koenver/ADE9000-ESP-32-energy-monitor-phasor-measurement-unit-modulair/hardware/pictures/IMG_0277.jpg

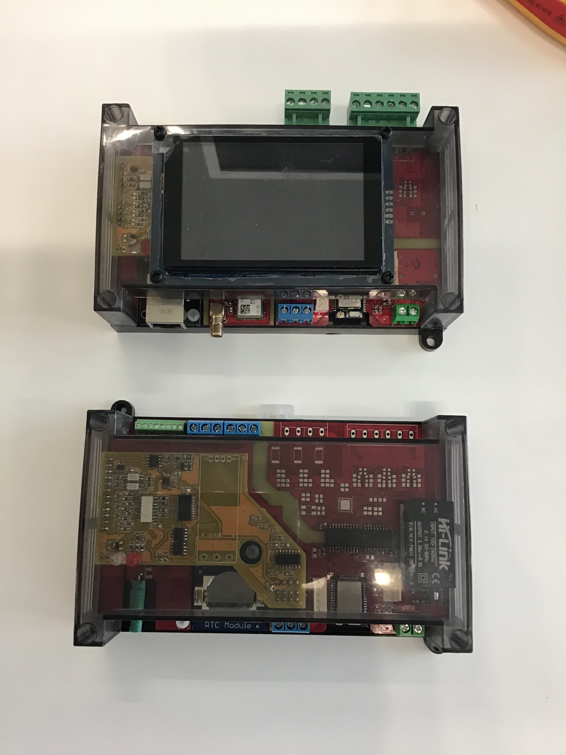
hardware/pictures/IMG_0277.jpg
