koenver/ADE9000-ESP-32-energy-monitor-phasor-measurement-unit-modulair/hardware/pictures/IMG_1338.JPG

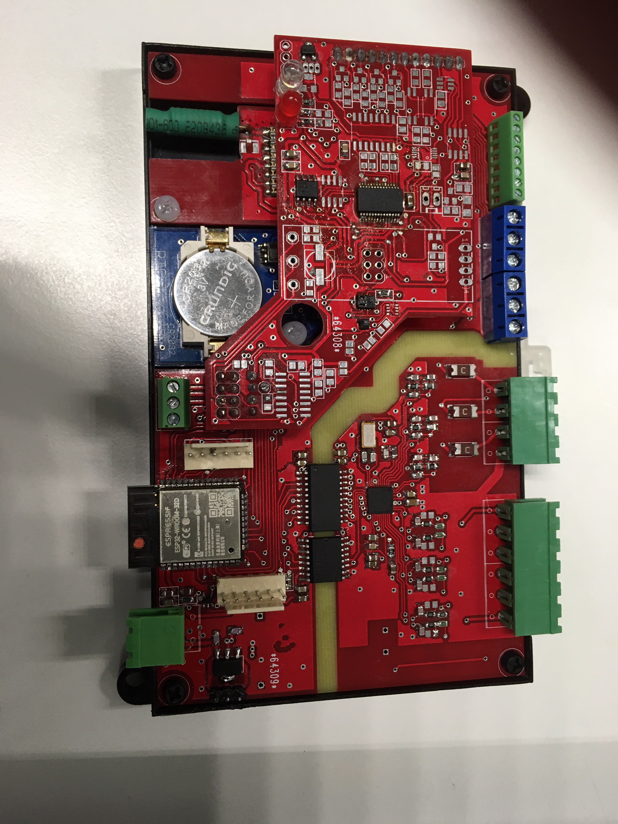
hardware/pictures/IMG_1338.JPG
