koenver/ADE9000-ESP-32-energy-monitor-phasor-measurement-unit-modulair/hardware/pictures/IMG_1339.JPG

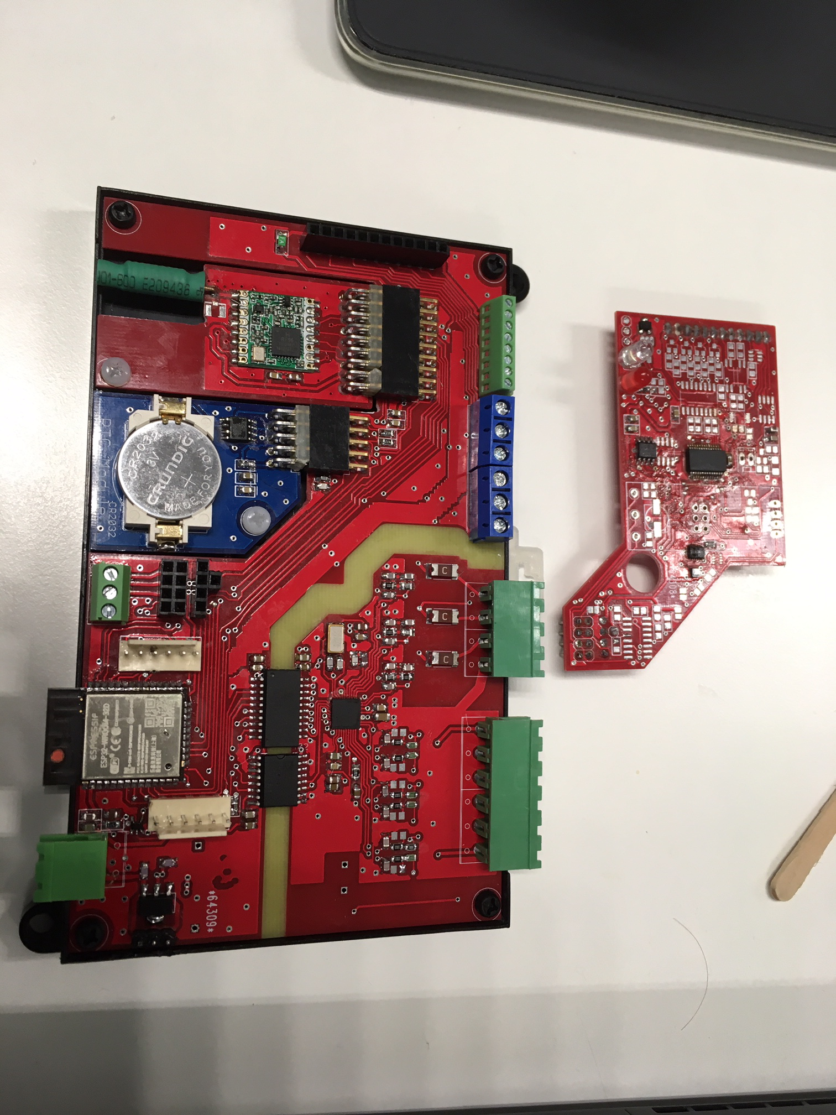
hardware/pictures/IMG_1339.JPG
