koenver/ADE9000-ESP-32-energy-monitor-phasor-measurement-unit-modulair/software/hardware tests/i2c test/I2C adress dump2.jpg

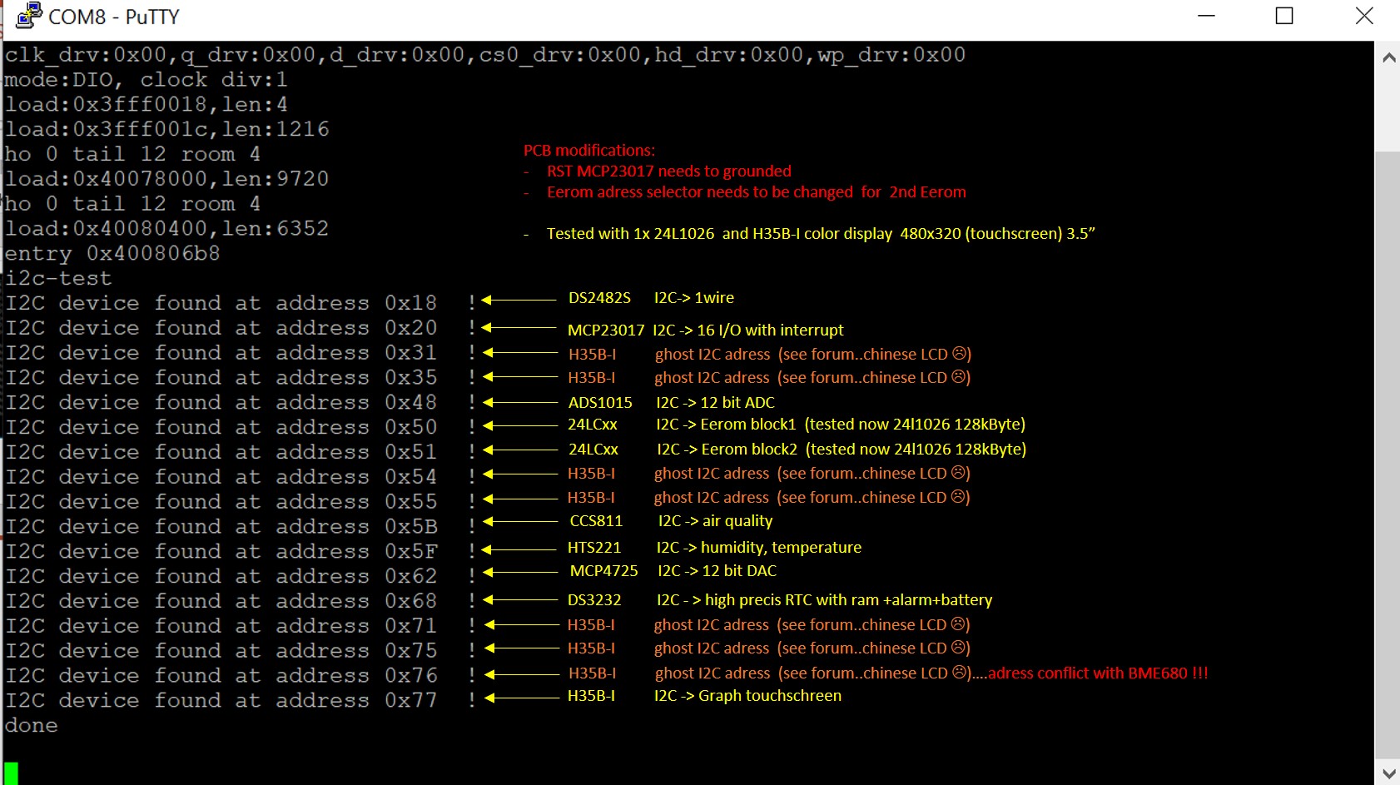
software/hardware tests/i2c test/I2C adress dump2.jpg
