koenver/ADE9000-ESP-32-energy-monitor-phasor-measurement-unit-modulair/software/hardware tests/lan8720 test/lan8720Apcb.jpg

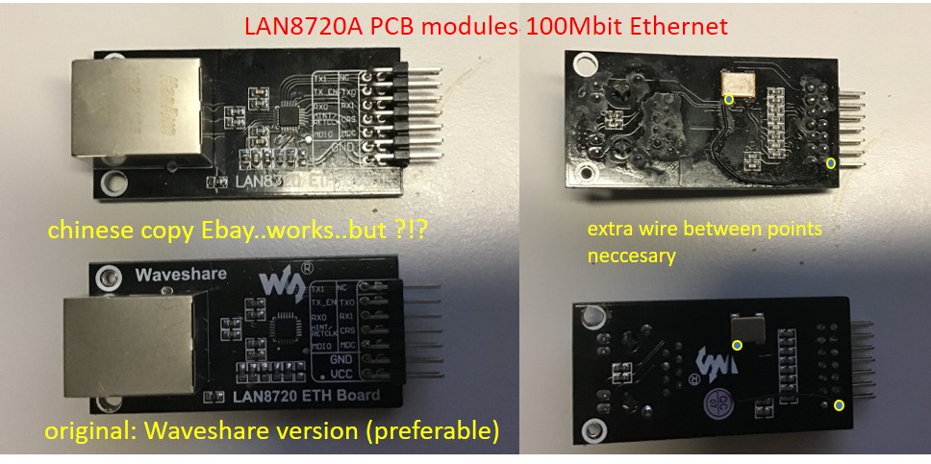
software/hardware tests/lan8720 test/lan8720Apcb.jpg
