koenver/ADE9000-ESP-32-energy-monitor-phasor-measurement-unit-modulair/software/hardware tests/MCP23017-IRQ-mCore-DS3232 test/tasks_core_0.ino

//****************** Core 0 main task (ADE9000) *********************************
void Core0_main( void * parameter )
{//***** setup part  ***
#ifdef DEBUG
  Serial.println("core0-main task:alive");
#endif

 //***** loop part   ***
 for(;;)
  {
   vTaskDelay(1);
  }
 vTaskDelete( NULL ); 
}
